nbp/uf2-batch-flasher/pcb/level1.kicad_sch

## KiCad design pcb/level1.kicad_sch (2023-11-12)

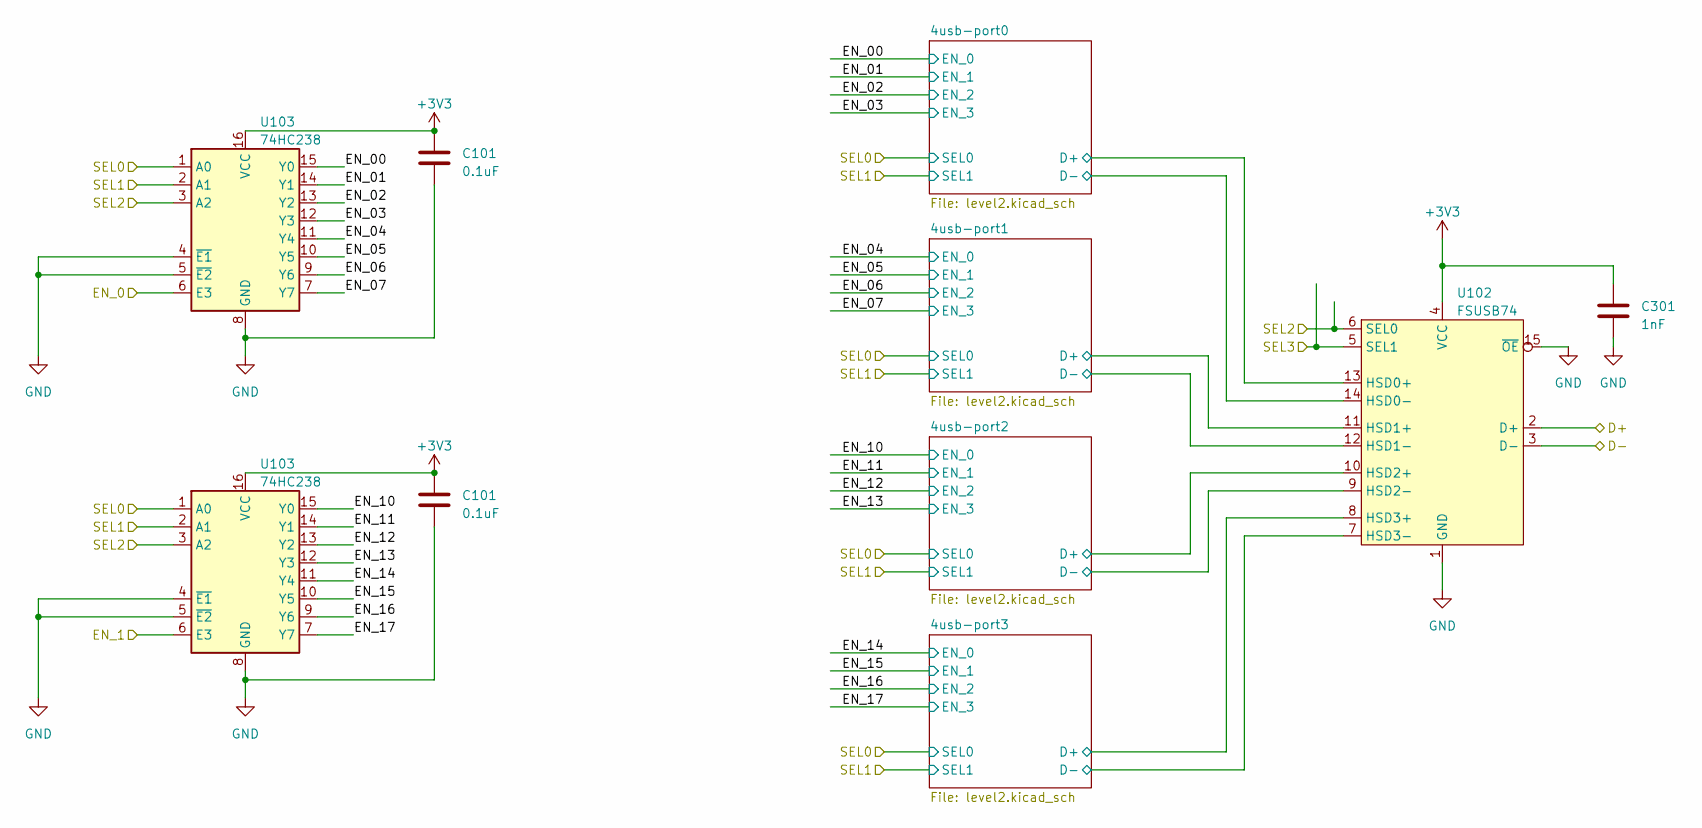
[picture p8: schematic level1.kicad_sch]

Parts:
C101: 0.1uF; C_0805_2012Metric
C301: 1nF; C_0603_1608Metric
U102: FSUSB74; UQFN-16_2.1x2.9mm_P0.4mm
U103: 74HC238; 74HC238 - SOIC-16

Connections:
+3V3: C101.1, C301.1, U102.4 (VCC), U103.16 (VCC)
D+: U102.2 (D+), U102.8 (HSD3+), U102.10 (HSD2+), U102.11 (HSD1+), U102.13 (HSD0+)
D-: U102.3 (D-), U102.7 (HSD3-), U102.9 (HSD2-), U102.12 (HSD1-), U102.14 (HSD0-)
EN_00: U103.15 (Y0)
EN_0: U103.6 (E3)
EN_1: U103.6 (E3)
EN_01: U103.14 (Y1)
EN_02: U103.13 (Y2)
EN_03: U103.12 (Y3)
EN_04: U103.11 (Y4)
EN_05: U103.10 (Y5)
EN_06: U103.9 (Y6)
EN_07: U103.7 (Y7)
EN_10: U103.15 (Y0)
EN_11: U103.14 (Y1)
EN_12: U103.13 (Y2)
EN_13: U103.12 (Y3)
EN_14: U103.11 (Y4)
EN_15: U103.10 (Y5)
EN_16: U103.9 (Y6)
EN_17: U103.7 (Y7)
GND: C101.2, C301.2, U102.1 (GND), U102.15 (~OE), U103.4 (~E1), U103.5 (~E2), U103.8 (GND)
SEL0: U103.1 (A0)
SEL1: U103.2 (A1)
SEL2: U102.6 (SEL0), U103.3 (A2)
SEL3: U102.5 (SEL1)
