nbp/uf2-batch-flasher/pcb/level2.kicad_sch

## KiCad design pcb/level2.kicad_sch (2023-11-12)

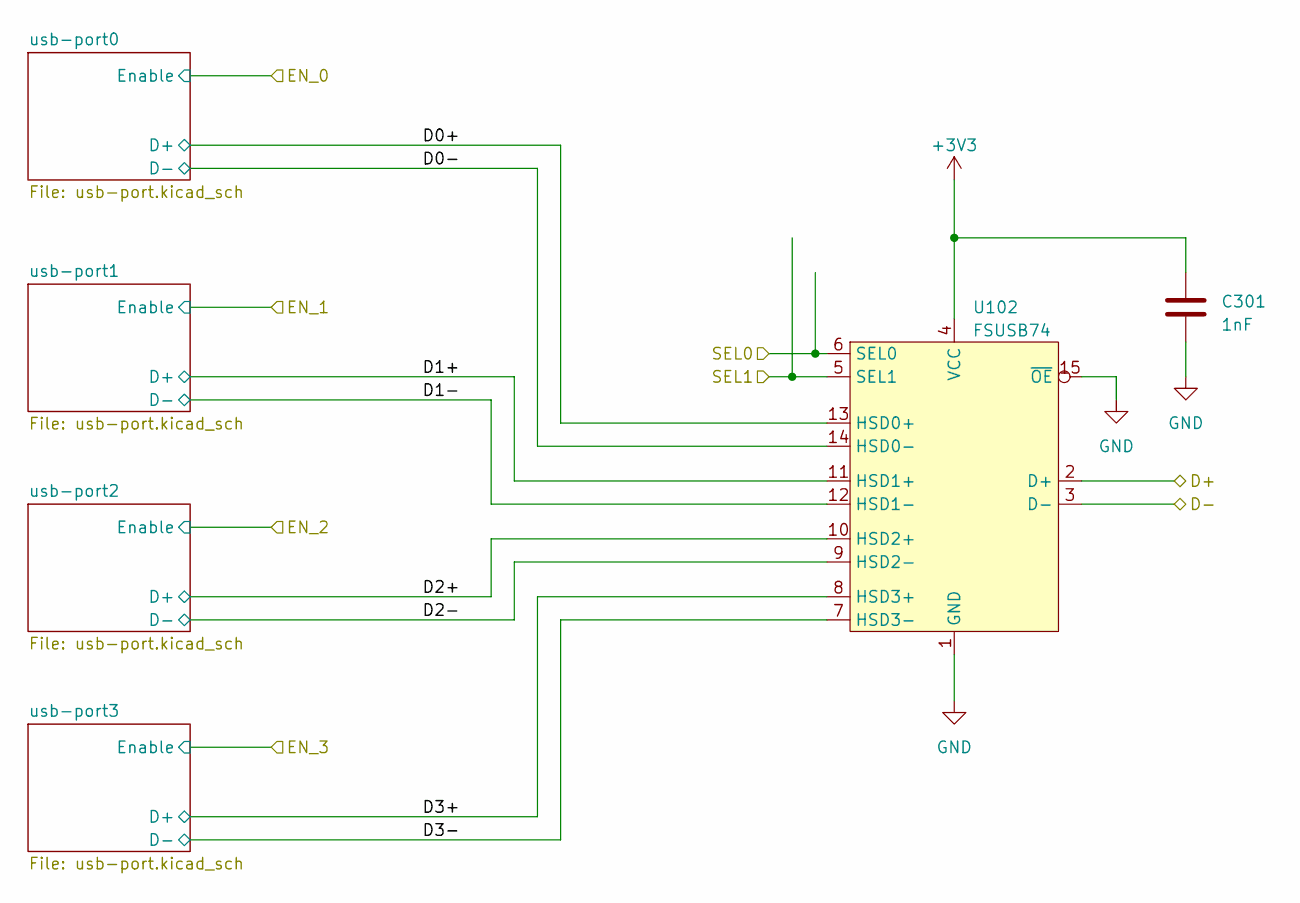
[picture p9: schematic level2.kicad_sch]

Parts:
C301: 1nF; C_0603_1608Metric
U102: FSUSB74; UQFN-16_2.1x2.9mm_P0.4mm

Connections:
+3V3: C301.1, U102.4 (VCC)
D0+: U102.13 (HSD0+)
D0-: U102.14 (HSD0-)
D1+: U102.11 (HSD1+)
D1-: U102.12 (HSD1-)
D2+: U102.10 (HSD2+)
D2-: U102.9 (HSD2-)
D3+: U102.8 (HSD3+)
D3-: U102.7 (HSD3-)
D+: U102.2 (D+)
D-: U102.3 (D-)
GND: C301.2, U102.1 (GND), U102.15 (~OE)
SEL0: U102.6 (SEL0)
SEL1: U102.5 (SEL1)
