nbp/uf2-batch-flasher/pcb/uf2-batch-flasher.kicad_sch

## KiCad design pcb/uf2-batch-flasher.kicad_sch (2023-11-12)

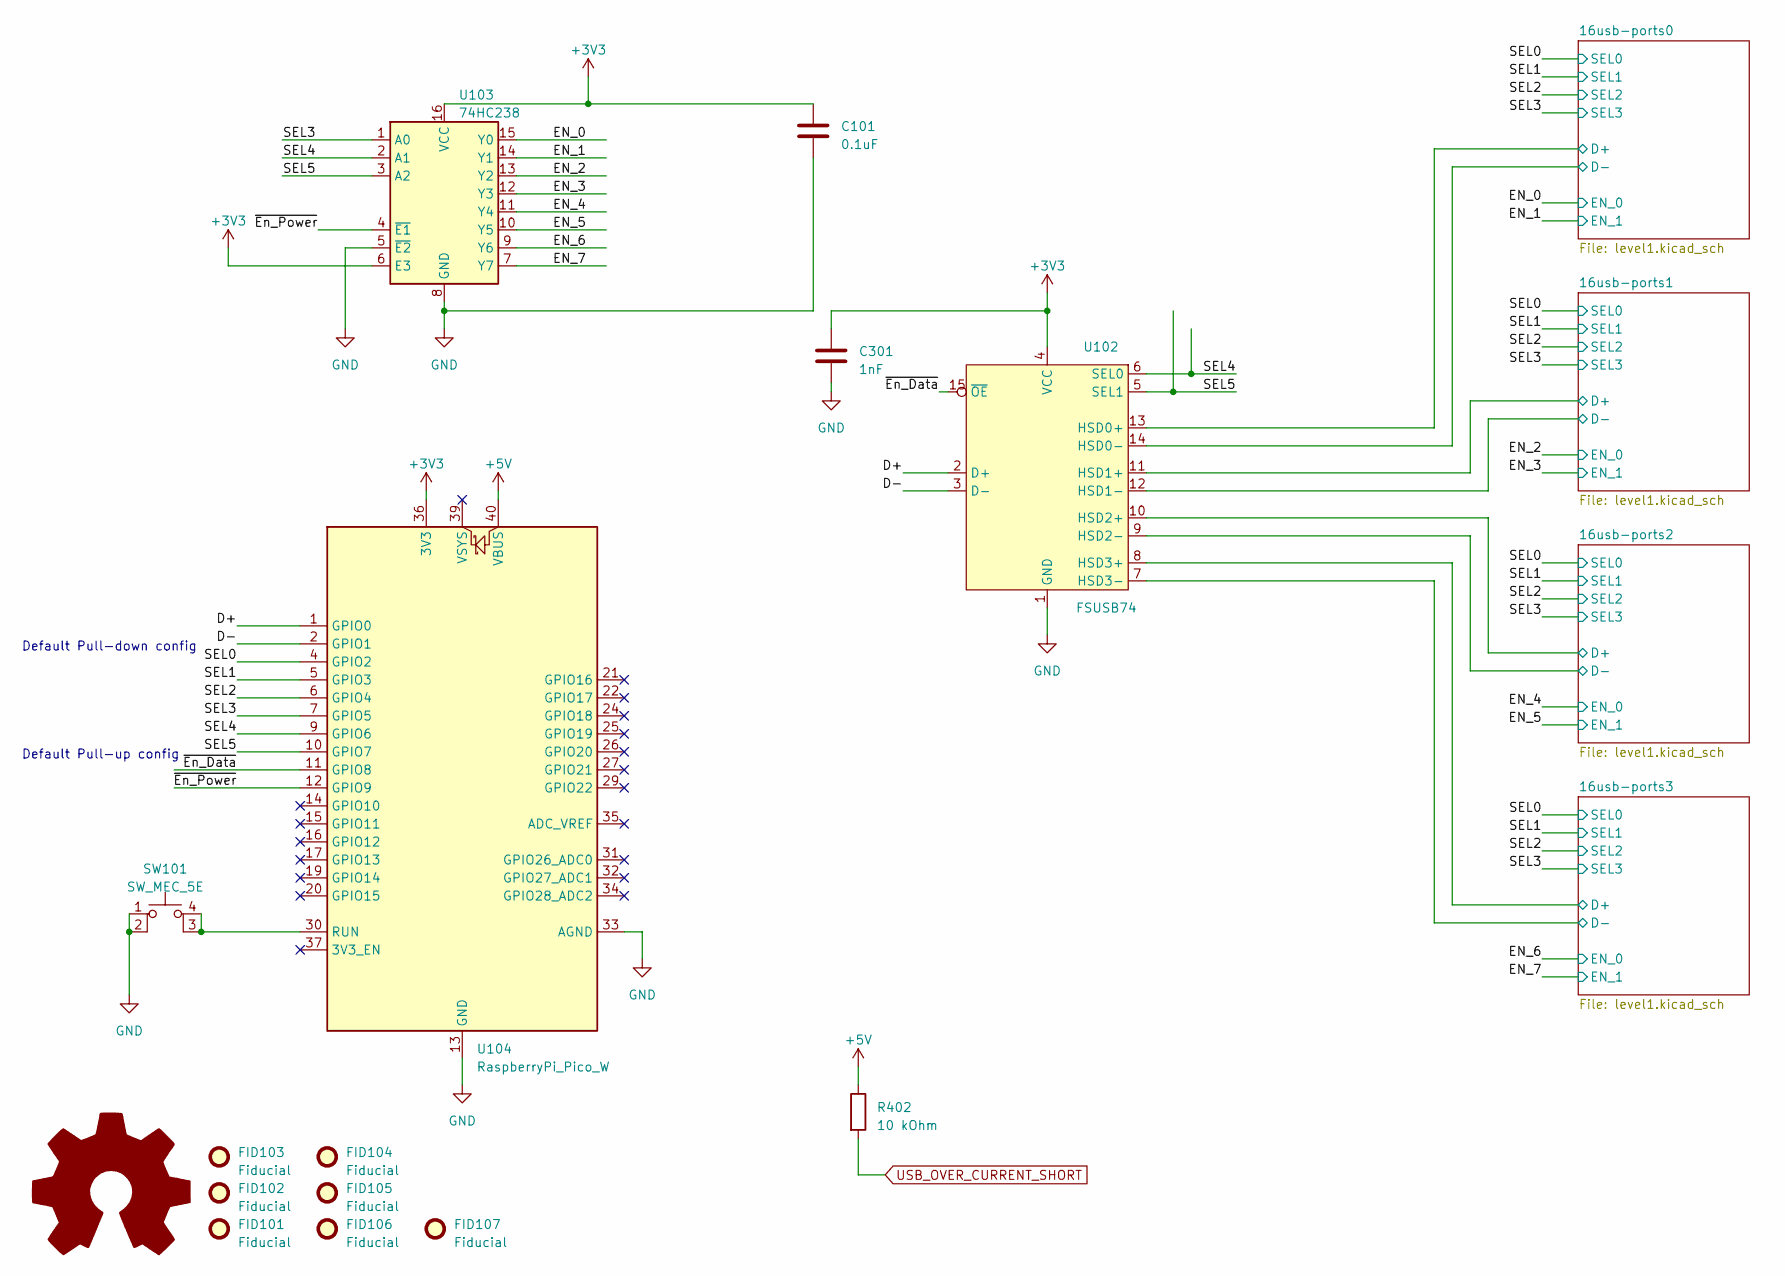
[picture p10: schematic uf2-batch-flasher.kicad_sch]

Parts:
C101: 0.1uF; C_0805_2012Metric
C301: 1nF; C_0603_1608Metric
FID101, FID102, FID103, FID104, FID105, FID106, FID107: Fiducial; Fiducial_1mm_Mask2mm
R402: 10 kOhm; R_0805_2012Metric
SW101: SW_MEC_5E; CUI_TS20
SYM101: Logo_Open_Hardware_Large; OSHW-Logo_11.4x12mm_SilkScreen
U102: FSUSB74; UQFN-16_2.1x2.9mm_P0.4mm
U103: 74HC238; 74HC238 - SOIC-16
U104: RaspberryPi_Pico_W; RaspberryPi_Pico_Common_THT_2

Connections:
+3V3: C101.1, C301.1, U102.4 (VCC), U103.6 (E3), U103.16 (VCC), U104.36 (3V3)
+5V: R402.1, U104.40 (VBUS)
D+: U102.2 (D+), U102.8 (HSD3+), U102.10 (HSD2+), U102.11 (HSD1+), U102.13 (HSD0+), U104.1 (GPIO0)
D-: U102.3 (D-), U102.7 (HSD3-), U102.9 (HSD2-), U102.12 (HSD1-), U102.14 (HSD0-), U104.2 (GPIO1)
EN_0: U103.15 (Y0)
EN_1: U103.14 (Y1)
EN_2: U103.13 (Y2)
EN_3: U103.12 (Y3)
EN_4: U103.11 (Y4)
EN_5: U103.10 (Y5)
EN_6: U103.9 (Y6)
EN_7: U103.7 (Y7)
GND: C101.2, C301.2, SW101.1, SW101.2, U102.1 (GND), U103.5 (~E2), U103.8 (GND), U104.3 (GND), U104.8 (GND), U104.13 (GND), U104.18 (GND), U104.23 (GND), U104.28 (GND), U104.33 (AGND), U104.38 (GND)
unnamed: SW101.3 (K), SW101.4 (A), U104.30 (RUN)
SEL0: U104.4 (GPIO2)
SEL1: U104.5 (GPIO3)
SEL2: U104.6 (GPIO4)
SEL3: U103.1 (A0), U104.7 (GPIO5)
SEL4: U102.6 (SEL0), U103.2 (A1), U104.9 (GPIO6)
SEL5: U102.5 (SEL1), U103.3 (A2), U104.10 (GPIO7)
USB_OVER_CURRENT_SHORT: R402.2
~En_Data: U102.15 (~OE), U104.11 (GPIO8)
~En_Power: U103.4 (~E1), U104.12 (GPIO9)

Notes on the sheet:
Default Pull-down config
Default Pull-up config
