nbp/uf2-batch-flasher/pcb/usb-port.kicad_sch

## KiCad design pcb/usb-port.kicad_sch (2023-11-12)

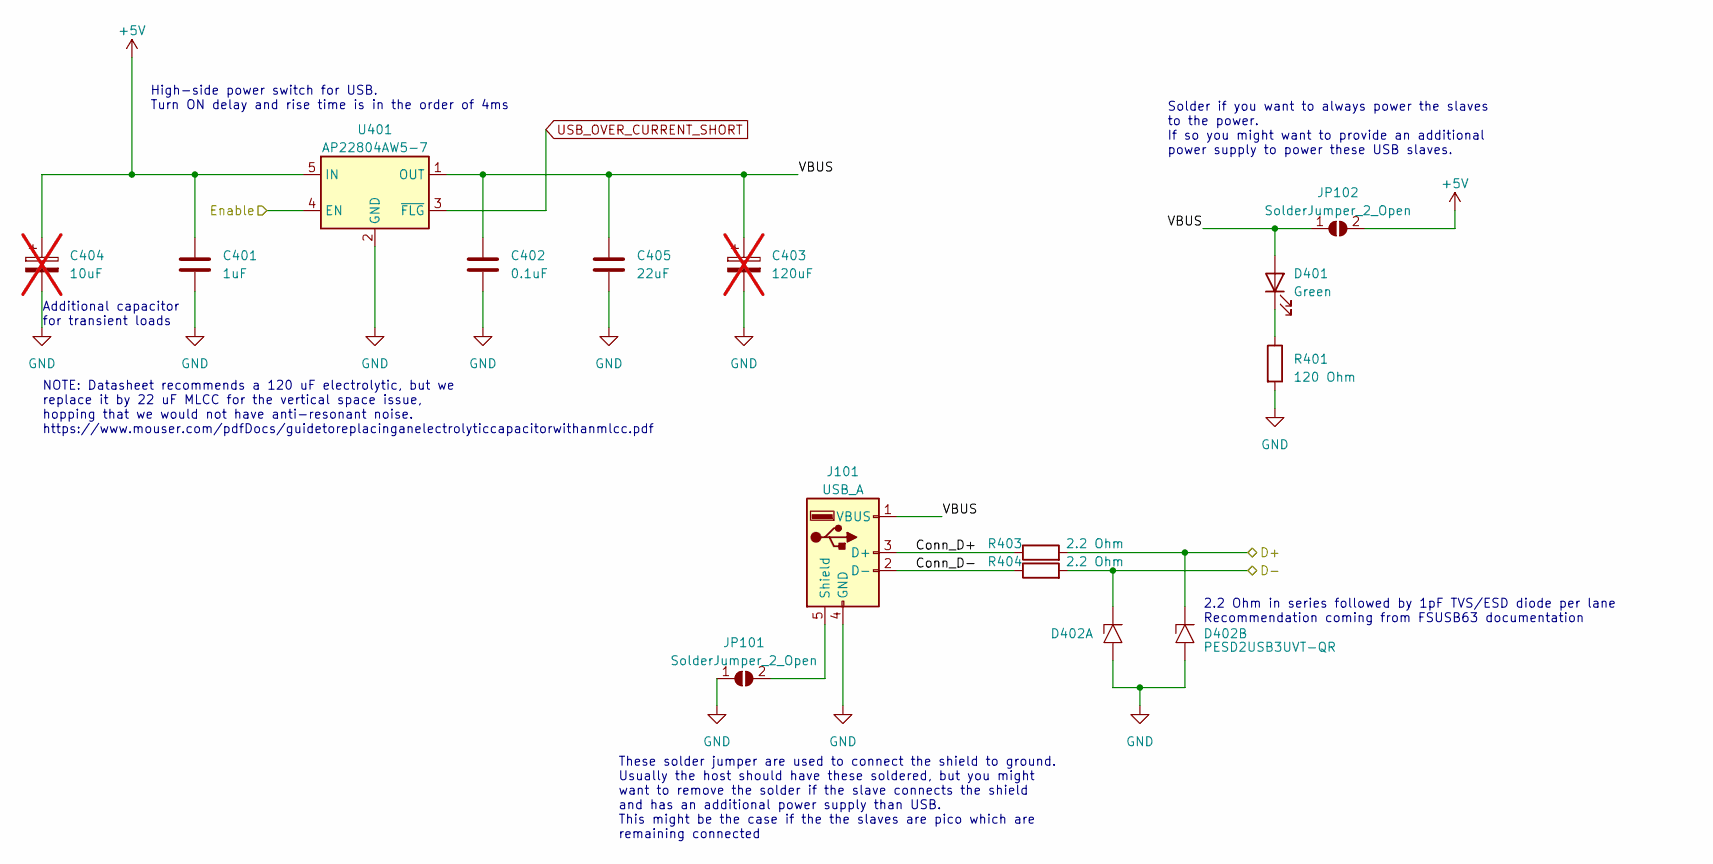
[picture p11: schematic usb-port.kicad_sch]

Parts:
C401: 1uF; C_0603_1608Metric
C402: 0.1uF; C_0805_2012Metric
C403: 120uF; CP_Radial_D5.0mm_P2.00mm; not fitted
C404: 10uF; CP_Radial_D5.0mm_P2.00mm; not fitted
C405: 22uF; C_0603_1608Metric
D401: Green; LED_0603_1608Metric
D402: PESD2USB3UVT-QR; SOT-23-3
J101: USB_A; USB A - GCT - USB1040 - Vertical
JP101, JP102: SolderJumper_2_Open; SolderJumper-2_P1.3mm_Open_RoundedPad1.0x1.5mm
R401: 120 Ohm; R_0603_1608Metric
R403, R404: 2.2 Ohm; R_0603_1608Metric
U401: AP22804AW5-7; SOT-23-5

Connections:
+5V: C401.1, C404.1, JP102.2 (B), U401.5 (IN)
Conn_D+: J101.3 (D+), R403.1
Conn_D-: J101.2 (D-), R404.1
D+: D402.2, R403.2
D-: D402.1, R404.2
Enable: U401.4 (EN)
GND: C401.2, C402.2, C403.2, C404.2, C405.2, D402.3, J101.4 (GND), JP101.1 (A), R401.2, U401.2 (GND)
unnamed: D401.1 (K), R401.1
unnamed: J101.5 (Shield), JP101.2 (B)
USB_OVER_CURRENT_SHORT: U401.3 (~FLG)
VBUS: C402.1, C403.1, C405.1, D401.2 (A), J101.1 (VBUS), JP102.1 (A), U401.1 (OUT)

Notes on the sheet:
Additional capacitor for transient loads
NOTE: Datasheet recommends a 120 uF electrolytic, but we replace it by 22 uF MLCC for the vertical space issue, hopping that we would not have anti-resonant noise. https://www.mouser.com/pdfDocs/guidetoreplacinganelectrolyticcapacitorwithanmlcc.pdf
2.2 Ohm in series followed by 1pF TVS/ESD diode per lane Recommendation coming from FSUSB63 documentation
High-side power switch for USB. Turn ON delay and rise time is in the order of 4ms
These solder jumper are used to connect the shield to ground. Usually the host should have these soldered, but you might want to remove the solder if the slave connects the shield and has an additional power supply than USB. This might be the case if the the slaves are pico which are remaining conn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
Solder if you want to always power the slaves to the power. If so you might want to provide an additional power supply to power these USB slaves.
