nbp/uf2-batch-flasher/firmware/web_server.c

#if !defined(USE_TCP_SERVER)

#include "hardware/watchdog.h"  // watchdog_reboot
#include "pico/bootrom.h" // reset_usb_boot

// Handle TCP and HTTP stacks.
#include "lwip/apps/httpd.h"

// Handle Wifi network setup.
#include "pico/cyw43_arch.h"

// Provide the pipe interface used to flash content to the USB device.
#include "pipe.h"

// Pipe interface used for stdio functions.
#include "stdio_web.h"

// Collect references to callback tasks.
#include "usb_host.h"

// Some debugging
#include "input.h"

#include "web_server.h"

// ---------------------------------------------------------
//  Dynamically Processed Content (CGI / GET request)

// Handle GET query, by giving the ?aaa=bb parameters as an array of params and
// values strings.
const char *select_cgi(int index, int num_params, char *params[], char *values[]) {
  for (int p = 0; p < num_params; p++) {
    const char *param = params[p];
    const char *value = values[p];
    if (strcmp(param, "active_device") == 0) {
      // Select a given USB port.
      intptr_t idx = (intptr_t) atoi(value);
      if (idx >= 0) {
        printf("Queue USB select_device: %u\n", idx);
        queue_usb_task(&select_device_cb, (void*) idx);
      } else {
        printf("Queue reset all USB status\n");
        queue_usb_task(&clear_usb_status_cb, (void*) 0);
      }
    }
  }
  return "/status.json";
}

const char *reboot_cgi(int index, int num_params, char *params[], char *values[]) {
  bool bootsel_reboot = false;
  for (int p = 0; p < num_params; p++) {
    const char *param = params[p];
    const char *value = values[p];
    if (strcmp(param, "bootsel") == 0) {
      uint32_t idx = (uint32_t) atoi(value);
      bootsel_reboot = idx;
    }
  }
  if (bootsel_reboot) {
    // Reboot in order to flash a new image.
    web_server_stop();
    reset_usb_boot(0, 0);
  } else {
    // Restart the program loaded in the flash.
    web_server_stop();
    watchdog_reboot(0, 0, 0);
    watchdog_enable(0, true);
  }
  // Not reachable !!!
  return "/status.json";
}

// List of CGI handlers, used to map a resource name to a handler to process the
// request.
static const tCGI cgi_handlers[] = {
  { "/select.cgi", select_cgi },
  { "/reboot.cgi", reboot_cgi }
};

void cgi_init() {
  http_set_cgi_handlers(cgi_handlers, LWIP_ARRAYSIZE(cgi_handlers));
}

// ---------------------------------------------------------
//  Dynamically Generated Content (SSI)

#define SSI_TAGS(_) \
  _(sts)            \
  _(out)

#define AS_STRING(name) #name ,
const char *ssi_tags[] = {
  SSI_TAGS(AS_STRING)
};

#define AS_ENUM(name) SSI_TAG__##name ,
enum {
  SSI_TAGS(AS_ENUM)
};

// The SSI handler intercept and substitute tags in files which are sent as a
// response. If a tag such as `/*# sts */` appears in one of the file, the
// following function would be called to replace the content by being called
// with the index being set to SSI_TAG__STS.
uint16_t ssi_handler(int index, char *insert_at, int ins_len) {
  size_t insert_len = (size_t) ins_len;
  int out_len = 0;
  int inc_len = 0;
  switch (index) {
  // Used in status.json
  case SSI_TAG__sts: {
    // Generate an array of integer where each index corresponds to one USB
    // device which can be selected by the USB host, and each value corresponds
    // of the last status code recorded while attempting to flash the device.
    inc_len = snprintf(insert_at, insert_len, "[");
    out_len += inc_len;
    insert_at += inc_len;
    insert_len -= (size_t) inc_len;
    size_t device = 0;
    for (; device < USB_DEVICES - 1; device++) {
      inc_len = snprintf(insert_at, insert_len, "%d,",
                         get_usb_device_status(device));
      out_len += inc_len;
      insert_at += inc_len;
      insert_len -= (size_t) inc_len;
    }
    inc_len = snprintf(insert_at, insert_len, "%d]",
                       get_usb_device_status(device));
    out_len += inc_len;
    insert_at += inc_len;
    insert_len -= (size_t) inc_len;
    break;
  }
  case SSI_TAG__out: {
    out_len = stdout_ssi(insert_at, ins_len);
    break;
  }
  default:
    return HTTPD_SSI_TAG_UNKNOWN;
  }
  LWIP_ASSERT("Sane length", (int) (uint16_t) out_len == out_len);
  return (uint16_t) out_len;
}

void ssi_init() {
  for (size_t t = 0; t < LWIP_ARRAYSIZE(ssi_tags); t++) {
    LWIP_ASSERT("Tags are restricted to LWIP_HTTPD_MAX_TAG_NAME_LEN",
                strlen(ssi_tags[t]) <= LWIP_HTTPD_MAX_TAG_NAME_LEN);
  }
  http_set_ssi_handler(ssi_handler, ssi_tags, LWIP_ARRAYSIZE(ssi_tags));
}

// ---------------------------------------------------------
//  Uploading Large Content (POST)

static void* current_connection = NULL;
static void* current_usb_context = NULL;
static bool pending_usb_error_report = false;
static bool pending_usb_request_flash = false;
static size_t total_bytes_received = 0;

void request_flash(void* arg)
{
  pending_usb_request_flash = true;
  current_usb_context = arg;
}

// Enabling LWIP_HTTPD_SUPPORT_POST in lwipopts.h implies that we have to define
// a few handlers which are expected by LwIP, namely httpd_post_begin,
// httpd_post_receive_data and httpd_post_finished.
err_t httpd_post_begin(void* connection, const char* uri, const char* http_request,
                       uint16_t http_request_len, int content_len, char* err_response_uri,
                       uint16_t err_response_uri_len, uint8_t* post_auto_wnd)
{
  printf("httpd_post_begin: %s\n", uri);
  LWIP_UNUSED_ARG(http_request);
  LWIP_UNUSED_ARG(http_request_len);
  LWIP_UNUSED_ARG(content_len);

  if (current_connection != NULL) {
    // One POST connection is still in progress, reject this new one until the
    // previous is finished.
    printf("Abort: One POST connection still in progress.\n");
    strncpy(err_response_uri, "/status.json", err_response_uri_len);
    return ERR_ABRT;
  }
  current_connection = connection;

#if LWIP_HTTPD_POST_MANUAL_WND
  // The network is faster than the flash, and the RAM of the usb host is
  // not enough to hold in memory what would be flashed. Thus we want to
  // throttle the speed manually.
  *post_auto_wnd = 0;
#else
  *post_auto_wnd = 1;
#endif

  // Match that the URI.
  if (strcmp(uri, "/flash") != 0) {
    printf("Abort: Unexpected URI.\n");
    strncpy(err_response_uri, "/status.json", err_response_uri_len);
    return ERR_ABRT;
  }

  printf("Preparing to stream content to the USB mass storage.\n");
  // TODO: transfer meta data, such as content_len or the file names.
  total_bytes_received = 0;
  pending_usb_error_report = false;
  queue_usb_task(&open_file, current_usb_context);
#ifdef USE_STREAM_FILE_CONTENT
  queue_usb_task(&stream_file_content, current_usb_context);
#else
#endif
  return ERR_OK;
}

void write_error(void* arg)
{
  pending_usb_error_report = true;
}

uint8_t* get_postmsg_buffer(void* arg)
{
  struct pbuf* p = (struct pbuf*) arg;
  return p->payload;
}

size_t get_postmsg_length(void* arg)
{
  struct pbuf* p = (struct pbuf*) arg;
  return p->len;
}

void free_postmsg(void* arg)
{
  struct pbuf* p = (struct pbuf*) arg;
  pbuf_free(p);
}

err_t httpd_post_receive_data(void* connection, struct pbuf* p)
{
  if (connection != current_connection) {
    printf("POST connection does not match.\n");
    return ERR_VAL;
  }
  if (pending_usb_error_report) {
    printf("POST connection aborted for USB error.\n");
    return ERR_ABRT;
  }

#ifdef USE_STREAM_FILE_CONTENT
  // Data would be dequeued by stream_file_content which is in charge of
  // writting it to the connected device.
  pipe_enqueue(p->payload, len);
  total_bytes_received += len;
#else
  total_bytes_received += p->len;
  struct pbuf* q = pbuf_clone(PBUF_TRANSPORT, PBUF_RAM, p);
  queue_usb_task(&write_file_content, (void*) q);
#endif

#if LWIP_HTTPD_POST_MANUAL_WND
  // Update the TCP window to throttle data reception.
  httpd_post_data_recved(connection, (uint16_t) len);
#endif
  pbuf_free(p);
  return ERR_OK;
}

void httpd_post_finished(void* connection, char* response_uri, uint16_t response_uri_len)
{
  if (connection != current_connection) {
    return;
  }

  queue_usb_task(&close_file, current_usb_context);
  printf("POST finished: received %u bytes.\n", total_bytes_received);

  const char* return_to = "/status.json";
  strncpy(response_uri, return_to, response_uri_len);
  current_connection = NULL;
  current_usb_context = NULL;
}

// ---------------------------------------------------------
//  Setup the Web Server

bool web_server_setup() {
  // Initializes the cyw43_driver and the lwIP stack.
  if (cyw43_arch_init()) {
    printf("Failure to initialize Wifi chip.\n");
    return false;
  }

  // Enables Wi-Fi Station (STA) mode, such that connections can be made to
  // other Wi-Fi Access Points.
  cyw43_arch_enable_sta_mode();

  // Connect to a wireless Access Point, block for a given period of time and
  // fails if the timeout is expired.
  //
  // TODO: Find a way such that we wait for configuring the device Wifi using
  // the Web interface. In which case we should probably wait on some default
  // public Wifi setup...
  printf("Connecting to Wi-Fi...\n");
  if (cyw43_arch_wifi_connect_timeout_ms(WIFI_SSID, WIFI_PASSWORD, CYW43_AUTH_WPA2_AES_PSK, 30000)) {
    printf("Failure to connect to the Wi-Fi network.\n");
    return false;
  }
  printf("Connected.\n");

  httpd_init();
  ssi_init();
  cgi_init();
  printf("HTTPD initialized.\n");
  return true;
}

void web_server_loop() {
  while (true) {
    cyw43_arch_poll();
    exec_web_task();
  }
}

void web_server_stop() {
  cyw43_arch_deinit();
}

#endif // !defined(USE_TCP_SERVER)
